speedypotato/chuni-lite/chunair-cad/IMG_20211214_130954.jpg

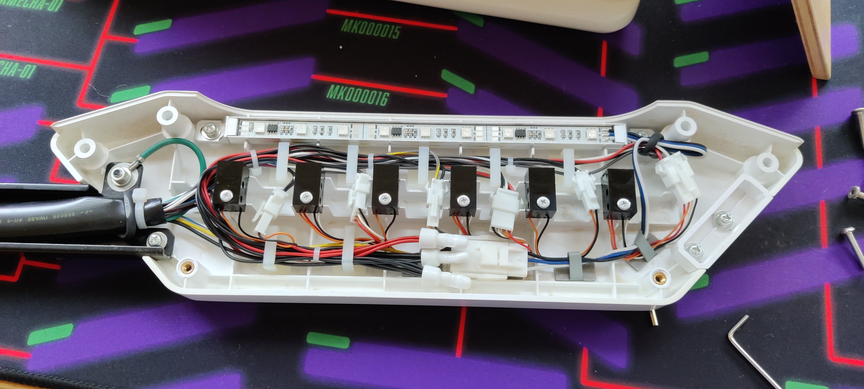
chunair-cad/IMG_20211214_130954.jpg
