speedypotato/chuni-lite/chunair-cad/IMG_20211214_131945.jpg

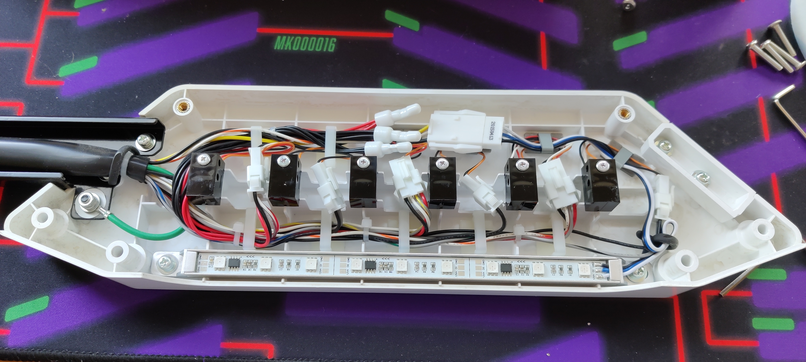
chunair-cad/IMG_20211214_131945.jpg
