speedypotato/chuni-lite/chunair-cad/IMG_20211214_160842.jpg

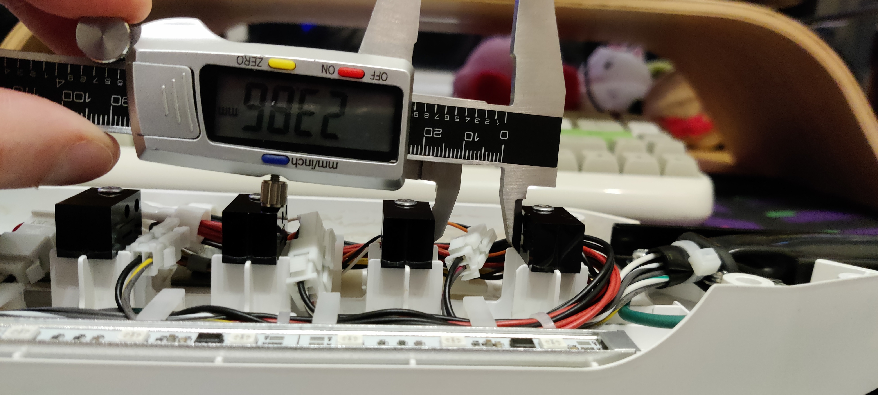
chunair-cad/IMG_20211214_160842.jpg
