speedypotato/chuni-lite/chunair-cad/IMG_20211214_160842__01.jpg

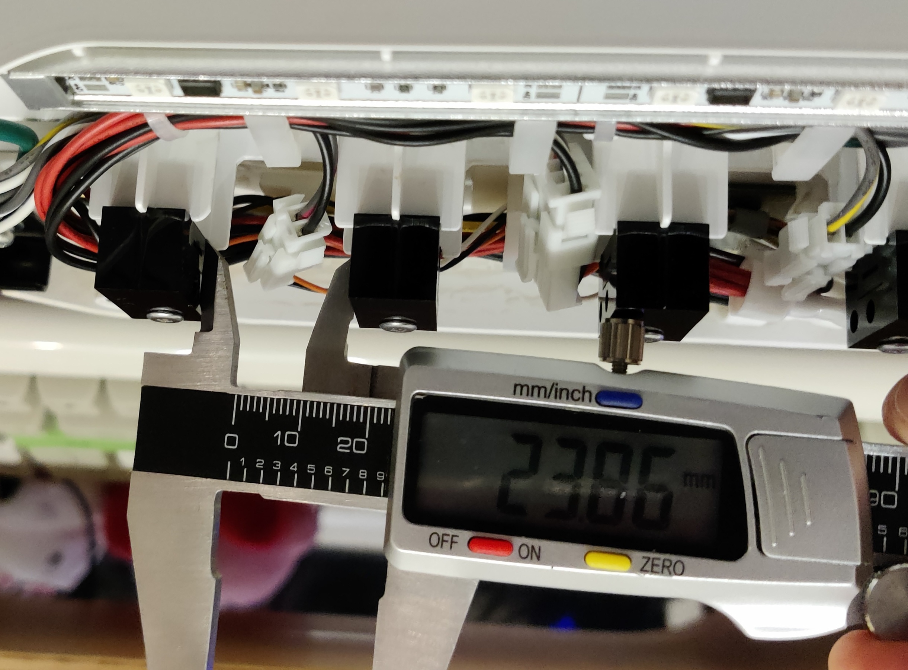
chunair-cad/IMG_20211214_160842__01.jpg
