speedypotato/chuni-lite/chunair-cad/IMG_20211214_161618.jpg

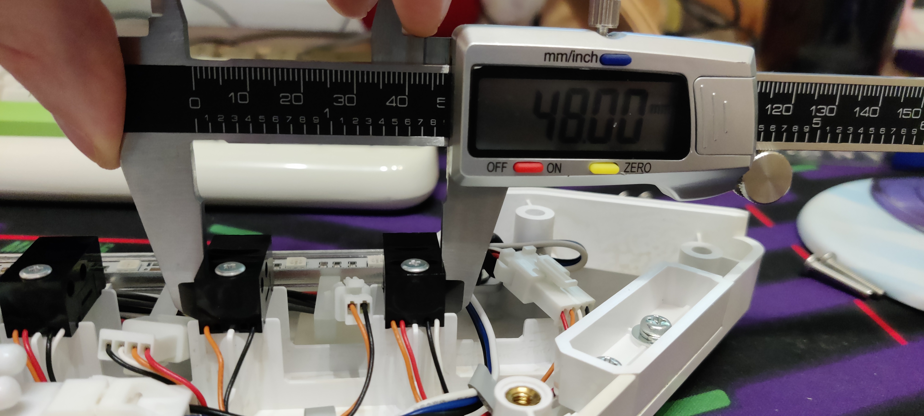
chunair-cad/IMG_20211214_161618.jpg
