speedypotato/chuni-lite/chunair-cad/airs/print/a12/bumper.3MF

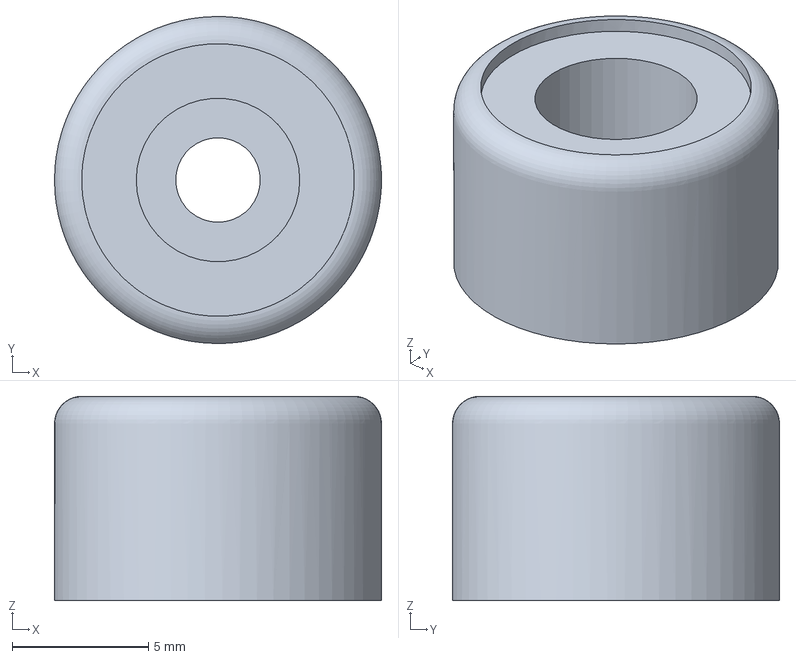
[picture p27: CAD file, 2022-03-22]
chunair-cad/airs/print/a12/bumper.3MF
12.0 x 12.0 x 7.50 mm
