speedypotato/chuni-lite/chunair-cad/airs/print/a3/slider.3MF

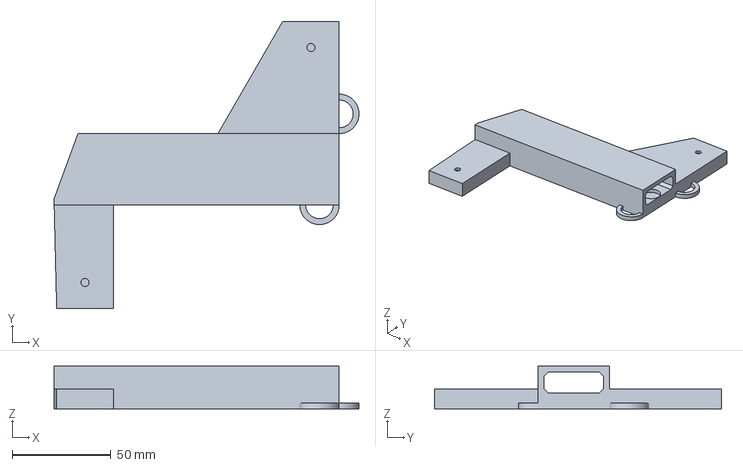
[picture p28: CAD file, 2022-02-23]
chunair-cad/airs/print/a3/slider.3MF
154.3 x 145.1 x 21.5 mm
