speedypotato/chuni-lite/chunair-cad/airs/print/a8/slider_rail.3MF

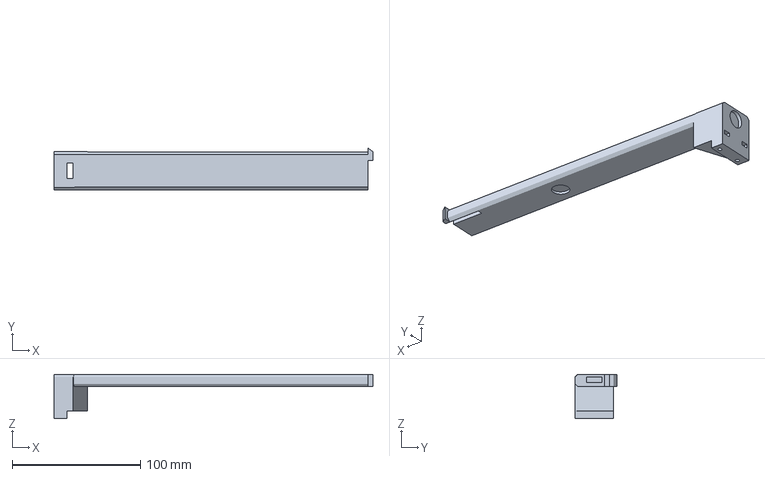
[picture p29: CAD file, 2022-02-23]
chunair-cad/airs/print/a8/slider_rail.3MF
249.0 x 33.0 x 34.5 mm
