speedypotato/chuni-lite/chunair/kicad-footprint-generator-master/scripts/Connector/Connector_JST/JST-PH-SMT-TOP_ENTRY.fcstd

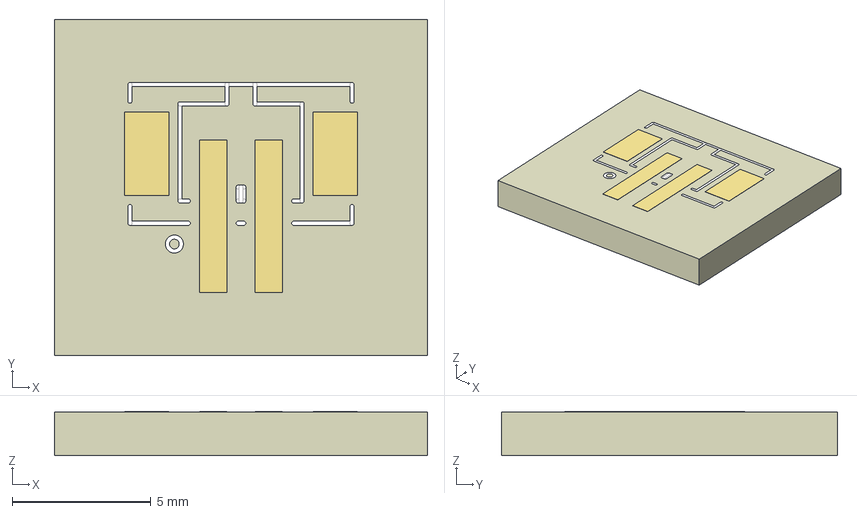
[picture p30: CAD file, 2022-02-25]
chunair/kicad-footprint-generator-master/scripts/Connector/Connector_JST/JST-PH-SMT-TOP_ENTRY.fcstd
13.4 x 12.1 x 1.60 mm
FrontSilk
TopPads
Pcb
