speedypotato/chuni-lite/chunair/kicad-footprint-generator-master/scripts/Connector/Connector_JST/JST-PH-SMT-SIDE_ENTRY.fcstd

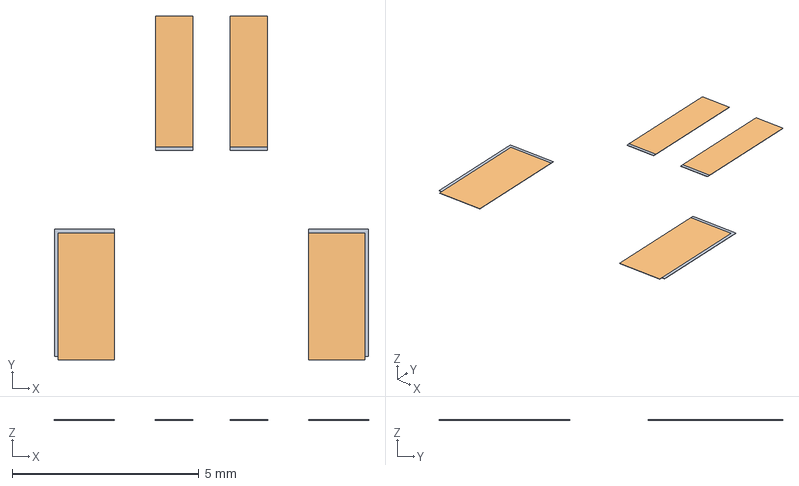
[picture p31: CAD file, 2022-02-25]
chunair/kicad-footprint-generator-master/scripts/Connector/Connector_JST/JST-PH-SMT-SIDE_ENTRY.fcstd
8.40 x 9.20 x 0.01 mm
TopPads
TopPads001
