speedypotato/chuni-lite/chunair-cad/parts/12x2mm_magnet.SLDPRT

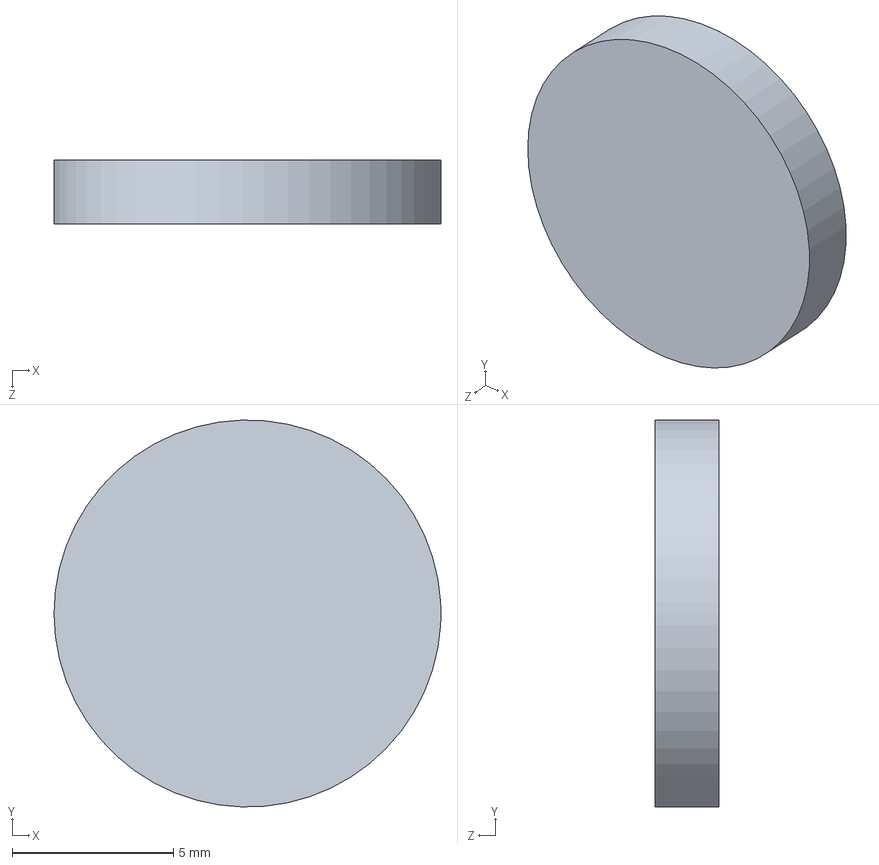
[picture p32: CAD file, 2022-02-10]
chunair-cad/parts/12x2mm_magnet.SLDPRT
12.0 x 12.0 x 2.00 mm
