speedypotato/chuni-lite/chunair/kicad-footprint-generator-master/scripts/Packages/Package_BGA/csp.yaml

WLCSP-12_1.403x1.555mm_P0.4mm_Stagger:
  description: "WLCSP-12, staggered array"
  size_source: "http://ww1.microchip.com/downloads/en/devicedoc/atmel-8235-8-bit-avr-microcontroller-attiny20_datasheet.pdf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"
  body_size_x: 1.403
  body_size_y: 1.555
  pitch_x: 0.2
  pitch_y: 0.346333
  pad_diameter: 0.215
  mask_margin: 0.0325
  paste_margin: 0.000001
  layout_x: 6
  layout_y: 4
  row_skips: [[2, 4, 6], [1, 3, 5], [2, 4, 6], [1, 3, 5]]
ST_WLCSP-25_Die425:
  description: "WLCSP-25"
  size_source: "http://www.st.com/resource/en/datasheet/stm32l031f6.pdf#page=112"
  body_size_x: 2.097
  body_size_y: 2.493
  pitch: 0.4
  pad_diameter: 0.22
  mask_margin: 0.04
  paste_margin: 0.000001
  layout_x: 5
  layout_y: 5
ST_WLCSP-25_Die444:
  description: "WLCSP-25"
  size_source: "http://www.st.com/resource/en/datasheet/stm32f031k6.pdf#page=93"
  body_size_x: 2.423
  body_size_y: 2.325
  pitch: 0.4
  pad_diameter: 0.225
  mask_margin: 0.0325
  paste_margin: 0.0125
  layout_x: 5
  layout_y: 5
ST_WLCSP-25_Die457:
  description: "WLCSP-25"
  size_source: "http://www.st.com/resource/en/datasheet/stm32l011k3.pdf#page=100"
  body_size_x: 2.133
  body_size_y: 2.070
  pitch: 0.4
  pad_diameter: 0.225
  mask_margin: 0.0325
  paste_margin: 0.0125
  layout_x: 5
  layout_y: 5
ST_WLCSP-36_Die417:
  description: "WLCSP-36"
  size_source: "http://www.st.com/resource/en/datasheet/stm32l052t8.pdf#page=123"
  body_size_x: 2.61
  body_size_y: 2.88
  pitch: 0.4
  pad_diameter: 0.22
  mask_margin: 0.04
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
  body_size_x: 5.537
  body_size_y: 6.095
  pitch: 0.4
  pad_diameter: 0.225
  mask_margin: 0.0325
  paste_margin: 0.0125
  layout_x: 13
  layout_y: 14
  row_skips: [[], [], [], [], [], [], [7], [7], [], [], [], [], [], []]
WLCSP-16_1.409x1.409mm_P0.35mm:
  description: "WLCSP-16"
  size_source: 'http://www.latticesemi.com/view_document?document_id=213'
  body_size_x: 1.409
  body_size_y: 1.409
  pitch: 0.35
  pad_diameter: 0.2
  layout_x: 4
  layout_y: 4
WLCSP-16_2.225x2.17mm_P0.5mm:
  description: "WLCSP-16 2.225x2.17mm"
  size_source: 'https://ww1.microchip.com/downloads/en/DeviceDoc/16B_WLCSP_CS_C04-06036c.pdf'
  body_size_x: 2.225
  body_size_y: 2.170
  pitch: 0.50
  pad_diameter: 0.327
  layout_x: 4
  layout_y: 4
WLCSP-8_1.551x2.284mm_P0.5mm:
  description: "WLCSP-8"
  size_source: "https://www.adestotech.com/wp-content/uploads/AT25SL321_112.pdf#page=75"
  body_size_x: 1.551
  body_size_y: 2.284
  pitch: 0.5
  pad_diameter: 0.2
  layout_x: 2
  layout_y: 4
WLCSP-4-X1-WLB0909-4_0.89x0.89mm_P0.5mm:
  description: "X1-WLB0909"
  size_source: 'https://www.diodes.com/assets/Datasheets/AP22913.pdf'
  body_size_x: 0.89
  body_size_y: 0.89
  pitch: 0.5
  pad_diameter: 0.235 # even though ball_diameter is 0.235 analog recommends a landing pad of 0.235
  layout_x: 2
  layout_y: 2
