speedypotato/chuni-lite/chunair/kicad-footprint-generator-master/scripts/Packages/Package_Gullwing__QFP_SOIC_SO/size_definitions/soic.yaml

FileHeader:
  library_Suffix: 'SO'
  device_type: 'SOIC'

SOIC-4_4.55x3.7mm_P2.54mm:
  custom_name_format: 'SOIC-4_4.55x3.7mm_P2.54mm' #does not take into account the excluded pins
  size_source: 'https://toshiba.semicon-storage.com/info/docget.jsp?did=11791&prodName=TLP185'
  body_size_x:
    minimum: 4.4
    nominal: 4.55
    maximum: 4.8
  body_size_y:
    minimum: 3.45
    nominal: 3.7
    maximum: 3.95
  overall_size_x:
    minimum: 6.6
    nominal: 7.0
    maximum: 7.4
  lead_width:
    nominal: 0.4
  lead_len:
    nominal: 0.5
  pitch: 1.27
  num_pins_x: 0
  num_pins_y: 3
  hidden_pins: [2, 5]

SOIC-4_4.55x2.6mm_P1.27mm:
  size_source: 'https://toshiba.semicon-storage.com/info/docget.jsp?did=12884&prodName=TLP291'
  body_size_x:
    minimum: 4.4
    nominal: 4.55
    maximum: 4.8
  body_size_y:
    minimum: 2.45
    nominal: 2.6
    maximum: 2.85
  overall_size_x:
    minimum: 6.6
    nominal: 7.0
    maximum: 7.4
  lead_width:
    minimum: 0.37
    maximum: 0.39
  lead_len:
    nominal: 0.5
  pitch: 1.27
  num_pins_x: 0
  num_pins_y: 2

SOIC-8_3.9x4.9mm_P1.27mm:
  size_source: 'JEDEC MS-012AA, https://www.analog.com/media/en/package-pcb-resources/package/pkg_pdf/soic_narrow-r/r_8.pdf'
  body_size_x: # from JEDEC
    nominal: 3.9
    tolerance: 0.1
  body_size_y:
    minimum: 4.8
    maximum: 5.0
  overall_height:
    minimum: 1.35
    maximum: 1.75

  overall_size_x: # from JEDEC (agrees with linked datasheet)
    nominal: 6
    tolerance: 0.2
  lead_len:
    minimum: 0.4
    maximum: 1.27
  lead_width: # from JEDEC (agrees with linked datasheet)
    minimum: 0.31
    maximum: 0.51

  pitch: 1.27
  num_pins_x: 0
  num_pins_y: 4

SOIC-8-1EP_3.9x4.9mm_P1.27mm_EP2.29x3.0mm:
  size_source: 'https://www.analog.com/media/en/technical-documentation/data-sheets/ada4898-1_4898-2.pdf#page=29'
  body_size_x:
    minimum: 3.8
    nominal: 3.9
    maximum: 4.0
  body_size_y:
    minimum: 4.8
    nominal: 4.9
    maximum: 5.0
  overall_height:
    minimum: 1.25
    maximum: 1.65

  overall_size_x:
    minimum: 5.8
    nominal: 6.0
    maximum: 6.2
  lead_len:
    minimum: 0.4
    maximum: 1.27
  lead_width:
    minimum: 0.31
    maximum: 0.51

  pitch: 1.27
  num_pins_x: 0
  num_pins_y: 4

  EP_size_x:
    nominal: 2.29
    tolerance: 0 # no tolerance given
  #EP_size_x_overwrite:
  #EP_mask_x:

  EP_size_y:
    nominal: 3.0 # 2.29+2*0.356 = 3.002 rounded to 3.0
    tolerance: 0 # no tolerance given
  #EP_size_y_overwrite:
  #EP_mask_y:

  # EP_paste_coverage: 0.65
  EP_num_paste_pads: [2, 2]

  thermal_vias:
    count: [2, 3]
    drill: 0.2
    # min_annular_ring: 0.15
    paste_via_clearance: 0.1
    EP_num_paste_pads: [2, 2]
    # paste_between_vias: 1
    # paste_rings_outside: 1
    EP_paste_coverage: 0.7
    grid: [1.3, 1]
    # bottom_pad_size:
    paste_avoid_via: False

SOIC-8-1EP_3.9x4.9mm_P1.27mm_EP2.41x3.81mm:
  size_source: 'https://www.analog.com/media/en/technical-documentation/data-sheets/ada4898-1_4898-2.pdf#page=29'
  body_size_x:
    minimum: 3.8
    nominal: 3.9
    maximum: 4.0
  body_size_y:
    minimum: 4.8
    nominal: 4.9
    maximum: 5.0
  overall_height:
    minimum: 1.25
    maximum: 1.65

  overall_size_x:
    minimum: 5.8
    nominal: 6.0
    maximum: 6.2
  lead_len:
    minimum: 0.4
    maximum: 1.27
  lead_width:
    minimum: 0.31
    maximum: 0.51

  pitch: 1.27
  num_pins_x: 0
  num_pins_y: 4

  EP_size_x:
    nominal: 2.41
    tolerance: 0 # no tolerance given
  # EP_size_x_overwrite: 2.41
  #EP_mask_x:

  EP_size_y:
    nominal: 3.81 # 3.098+2*0.356
    tolerance: 0 # no tolerance given
  # EP_size_y_overwrite: 3.1
  #EP_mask_y:

  # EP_paste_coverage: 0.65
  EP_num_paste_pads: [2, 2]

  thermal_vias:
    count: [2, 3]
    drill: 0.2
    # min_annular_ring: 0.15
    paste_via_clearance: 0.1
    EP_num_paste_pads: [2, 2]
    # paste_between_vias: 1
    # paste_rings_outside: 1
    EP_paste_coverage: 0.7
    grid: [1.4, 1.4]
    # bottom_pad_size:
    paste_avoid_via: False

SOIC-8-1EP_3.9x4.9mm_P1.27mm_EP2.41x3.1mm:
  size_source: 'http://www.ti.com/lit/ds/symlink/lm5017.pdf#page=31'
  body_size_x:
    minimum: 3.8
    maximum: 4.0
  body_size_y:
    minimum: 4.8
    maximum: 5.0
  overall_height:
    maximum: 1.7

  overall_size_x:
    minimum: 5.8
    maximum: 6.2
  lead_len:
    minimum: 0.4
    maximum: 1.27
  lead_width:
    minimum: 0.31
    maximum: 0.51

  pitch: 1.27
  num_pins_x: 0
  num_pins_y: 4

  EP_size_x:
    minimum: 2.11
    maximum: 2.71
  EP_size_x_overwrite: 2.95
  EP_mask_x: 2.71

  EP_size_y:
    minimum: 2.8
    maximum: 3.4
  EP_size_y_overwrite: 4.9
  EP_mask_y: 3.4

  # EP_paste_coverage: 0.65
  EP_num_paste_pads: [2, 2]

  thermal_vias:
    count: [2, 4]
    drill: 0.2
    # min_annular_ring: 0.15
    paste_via_clearance: 0.1
    EP_num_paste_pads: [2, 2]
    # paste_between_vias: 1
    # paste_rings_outside: 1
    EP_paste_coverage: 0.7
    grid: [1.3, 1.3]
    # bottom_pad_size:
    paste_avoid_via: False

SOIC-8-1EP_3.9x4.9mm_P1.27mm_EP2.41x3.3mm:
  size_source: 'http://www.allegromicro.com/~/media/Files/Datasheets/A4950-Datasheet.ashx#page=8'
  body_size_x:
    nominal: 3.9
    tolerance: 0.1
  body_size_y:
    nominal: 4.9
    tolerance: 0.1
  overall_height:
    maximum: 1.7

  overall_size_x:
    nominal: 6.0
    tolerance: 0.2
  lead_len:
    minimum: 0.4
    maximum: 1.27
  lead_width:
    minimum: 0.31
    maximum: 0.51

  pitch: 1.27
  num_pins_x: 0
  num_pins_y: 4

  EP_size_x:
    nominal: 2.41
    tolerance: 0 # no tolerance given
  # EP_size_x_overwrite: 2.41
  #EP_mask_x:

  EP_size_y:
    nominal: 3.3
    tolerance: 0 # no tolerance given
  # EP_size_y_overwrite: 3.1
  #EP_mask_y:

  # EP_paste_coverage: 0.65
  EP_num_paste_pads: [2, 2]

  thermal_vias:
    count: [2, 3]
    drill: 0.2
    # min_annular_ring: 0.15
    paste_via_clearance: 0.1
    EP_num_paste_pads: [2, 2]
    # paste_between_vias: 1
    # paste_rings_outside: 1
    EP_paste_coverage: 0.7
    grid: [1.4, 1.2]
    # bottom_pad_size:
    paste_avoid_via: False

SOIC-8-1EP_3.9x4.9mm_P1.27mm_EP2.514x3.2mm:
  size_source: 'https://www.renesas.com/eu/en/www/doc/datasheet/hip2100.pdf#page=13'
  body_size_x:
    minimum: 3.8 # rounded from 3.811
    maximum: 4.0 # rounded from 3.99
  body_size_y:
    minimum: 4.8
    maximum: 5.0 # rounded from 4.98
  overall_height:
    minimum: 1.43
    maximum: 1.68

  overall_size_x:
    minimum: 5.84
    maximum: 6.2
  lead_len:
    minimum: 0.41
    maximum: 0.89
  lead_width:
    minimum: 0.35
    maximum: 0.49

  pitch: 1.27
  num_pins_x: 0
  num_pins_y: 4

  EP_size_x:
    nominal: 2.514 # only maximum given but that is not supported by the script
    tolerance: 0
  # EP_size_x_overwrite:
  #EP_mask_x:

  EP_size_y:
    nominal: 3.2 # only maximum given but that is not supported by the script
    tolerance: 0
  # EP_size_y_overwrite:
  #EP_mask_y:

  # EP_paste_coverage: 0.65
  EP_num_paste_pads: [2, 2]

  thermal_vias:
    count: [2, 3]
    drill: 0.2
    # min_annular_ring: 0.15
    paste_via_clearance: 0.1
    EP_num_paste_pads: [2, 2]
    # paste_between_vias: 1
    # paste_rings_outside: 1
    EP_paste_coverage: 0.7
    grid: [1.4, 1.0]
    # bottom_pad_size:
    paste_avoid_via: False

    
       
SOIC-8-1EP_3.9x4.9mm_P1.27mm_EP2.62x3.51mm:
  size_source: 'https://www.monolithicpower.com/en/documentview/productdocument/index/version/2/document_type/Datasheet/lang/en/sku/MP2303A/document_id/494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'
  body_size_x:
    minimum: 3.8
    maximum: 4.0
  body_size_y:
    minimum: 4.8
    maximum: 5.0
  overall_height:
    minimum: 1.3
    maximum: 1.7

  overall_size_x:
    minimum: 5.8
    maximum: 6.2
  lead_len:
    minimum: 0.41
    maximum: 1.27
  lead_width:
    minimum: 0.33
    maximum: 0.51

  pitch: 1.27
  num_pins_x: 0
  num_pins_y: 4

  EP_size_x:
    minimum: 2.26
    maximum: 2.56

  EP_size_y:
    minimum: 3.15
    maximum: 3.45

  EP_size_x_overwrite: 2.62
  EP_size_y_overwrite: 3.51

  # EP_paste_coverage: 0.65
  EP_num_paste_pads: [2, 2]

  thermal_vias:
    count: [2, 3]
    drill: 0.2
    # min_annular_ring: 0.15
    paste_via_clearance: 0.1
    EP_num_paste_pads: [2, 2]
    # paste_between_vias: 1
    # paste_rings_outside: 1
    EP_paste_coverage: 0.7
    grid: [1.4, 1.0]
    # bottom_pad_size:
    paste_avoid_via: False

    
    
SOIC-8_5.23x5.23mm_P1.27mm:
  size_source: 'http://www.winbond.com/resource-files/w25q32jv%20revg%2003272018%20plus.pdf#page=68'
  body_size_x:
    minimum: 5.13
    nominal: 5.23
    maximum: 5.33
  body_size_y:
    minimum: 5.13
    nominal: 5.23
    maximum: 5.33
  overall_height:
    minimum: 1.75
    nominal: 1.95
    maximum: 2.16

  overall_size_x:
    minimum: 7.7
    nominal: 7.9
    maximum: 8.1
  lead_len:
    minimum: 0.5
    nominal: 0.65
    maximum: 0.8
  lead_width:
    minimum: 0.35
    nominal: 0.42
    maximum: 0.48

  pitch: 1.27
  num_pins_x: 0
  num_pins_y: 4

SOIC-8_5.275x5.275mm_P1.27mm:
  size_source: 'http://ww1.microchip.com/downloads/en/DeviceDoc/20005045C.pdf#page=23'
  body_size_x:
    minimum: 5.15
    maximum: 5.4
  body_size_y:
    minimum: 5.15
    maximum: 5.4
  overall_size_x:
    minimum: 7.7
    maximum: 8.1
  overall_height:
    minimum: 1.75
    maximum: 2.16
  lead_width:
    minimum: 0.35
    maximum: 0.5
  lead_len:
    minimum: 0.5
    maximum: 0.8

  pitch: 1.27
  num_pins_x: 0
  num_pins_y: 4

SOIC-8_7.5x5.85mm_P1.27mm:
  size_source: 'http://www.ti.com/lit/ml/mpds382b/mpds382b.pdf'
  body_size_x:
    minimum: 7.4
    maximum: 7.6
  body_size_y:
    minimum: 5.75
    maximum: 5.95
  overall_height:
    maximum: 2.8
  overall_size_x:
    nominal: 11.5
    tolerance: 0.25
  lead_len:
    minimum: 0.5
    maximum: 1.0
  lead_width:
    minimum: 0.31
    maximum: 0.51

  pitch: 1.27
  num_pins_x: 0
  num_pins_y: 4

SOIC-14_3.9x8.7mm_P1.27mm:
  #round to two significant digits to comply with old name
  custom_name_format: SOIC-{pincount}_{size_x:.2g}x{size_y:.2g}mm_P{pitch:g}mm
  size_source: 'JEDEC MS-012AB, https://www.analog.com/media/en/package-pcb-resources/package/pkg_pdf/soic_narrow-r/r_14.pdf'
  body_size_x: # from JEDEC
    nominal: 3.9
    tolerance: 0.1
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
    minimum: 2.35
    maximum: 2.65

  overall_size_x: # from JEDEC
    nominal: 10.3
    tolerance: 0.33
  lead_len:
    minimum: 0.4
    maximum: 1.27
  lead_width: # from JEDEC (agrees with linked datasheet)
    minimum: 0.31
    maximum: 0.51

  pitch: 1.27
  num_pins_x: 0
  num_pins_y: 14

SOIC-28W_7.5x18.7mm_P1.27mm:
  #round to two significant digits to comply with old name
  custom_name_format: SOIC-{pincount}W_{size_x:.2g}x{size_y:.3g}mm_P{pitch:g}mm
  size_source: 'https://www.akm.com/akm/en/file/datasheet/AK5394AVS.pdf#page=23'
  body_size_x:
    nominal: 7.5
    tolerance: 0.2
  body_size_y:
    nominal: 18.7
    tolerance: 0.3
  overall_height:
    nominal: 2.2
    tolerance: 0.1

  overall_size_x:
    nominal: 10.4
    tolerance: 0.3
  lead_len:
    nominal: 0.75
    tolerance: 0.2
  lead_width:
    nominal: 0.4
    tolerance: 0.1

  pitch: 1.27
  num_pins_x: 0
  num_pins_y: 14
