speedypotato/chuni-lite/chunair/kicad-footprint-generator-master/scripts/Packages/Package_Gullwing__QFP_SOIC_SO/size_definitions/tssop.yaml

FileHeader:
  library_Suffix: 'SO'
  device_type: 'TSSOP'

##############################################################################
# TSSOP Variations - 0.40 PITCH
# BODY WIDTH (E1) = 4.40 NOM
##############################################################################

TSSOP-14_4.4x3.6mm_P0.4mm:
  size_source: 'JEDEC MO-194 Var AA https://www.jedec.org/document_search?search_api_views_fulltext=MO-194'
  body_size_x: 4.4 +/-0.1
  body_size_y: 3.6 +/-0.1
  overall_size_x: 6.4
  body_height: 1.2
  lead_width: 0.13 .. 0.23
  lead_len: 0.6 +/-0.15
  pitch: 0.4
  num_pins_x: 0
  num_pins_y: 7

TSSOP-16_4.4x3.6mm_P0.4mm:
  size_source: 'JEDEC MO-194 Var AB https://www.jedec.org/document_search?search_api_views_fulltext=MO-194'
  body_size_x: 4.4 +/-0.1
  body_size_y: 3.6 +/-0.1
  overall_size_x: 6.4
  body_height: 1.2
  lead_width: 0.13 .. 0.23
  lead_len: 0.6 +/-0.15
  pitch: 0.4
  num_pins_x: 0
  num_pins_y: 8

TSSOP-20_4.4x5mm_P0.4mm:
  size_source: 'JEDEC MO-194 Var AC https://www.jedec.org/document_search?search_api_views_fulltext=MO-194'
  body_size_x: 4.4 +/-0.1
  body_size_y: 5.0 +/-0.1
  overall_size_x: 6.4
  body_height: 1.2
  lead_width: 0.13 .. 0.23
  lead_len: 0.6 +/-0.15
  pitch: 0.4
  num_pins_x: 0
  num_pins_y: 10

TSSOP-24_4.4x5mm_P0.4mm:
  size_source: 'JEDEC MO-153 Var CA https://www.jedec.org/document_search?search_api_views_fulltext=MO-153'
  body_size_x: 4.4 +/-0.1
  body_size_y: 5.0 +/-0.1
  overall_size_x: 6.4
  body_height: 1.2
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
  body_size_x: 8.0 +/-0.1
  body_size_y: 12.5 +/-0.1
  overall_size_x: 10.0
  body_height: 1.2
  lead_width: 0.17 .. 0.30
  lead_len: 0.6 +/-0.15
  pitch: 0.5
  num_pins_x: 0
  num_pins_y: 24

TSSOP-56_8x14mm_P0.5mm:
  size_source: 'JEDEC MO-153 Var HD https://www.jedec.org/document_search?search_api_views_fulltext=MO-153'
  body_size_x: 8.0 +/-0.1
  body_size_y: 14.0 +/-0.1
  overall_size_x: 10.0
  body_height: 1.2
  lead_width: 0.17 .. 0.30
  lead_len: 0.6 +/-0.15
  pitch: 0.5
  num_pins_x: 0
  num_pins_y: 28

##############################################################################
# TSSOP Variations - 0.65 PITCH
# BODY WIDTH (E1) = 4.40 NOM
##############################################################################

TSSOP-8_4.4x3mm_P0.65mm:
  size_source: 'JEDEC MO-153 Var AA https://www.jedec.org/document_search?search_api_views_fulltext=MO-153'
  body_size_x: 4.4 +/-0.1
  body_size_y: 3.0 +/-0.1
  overall_size_x: 6.4
  body_height: 1.2
  lead_width: 0.17 .. 0.30
  lead_len: 0.6 +/-0.15
  pitch: 0.65
  num_pins_x: 0
  num_pins_y: 4

TSSOP-16_4.4x5mm_P0.65mm:
  size_source: 'JEDEC MO-153 Var AB https://www.jedec.org/document_search?search_api_views_fulltext=MO-153'
  body_size_x: 4.4 +/-0.1
  body_size_y: 5.0 +/-0.1
  overall_size_x: 6.4
  body_height: 1.2
  lead_width: 0.17 .. 0.30
  lead_len: 0.6 +/-0.15
  pitch: 0.65
  num_pins_x: 0
  num_pins_y: 8

TSSOP-16-1EP_4.4x5mm_P0.65mm_EP3x3mm:
  size_source: 'Allegro A4954 https://www.allegromicro.com/-/media/Files/Datasheets/A4954-Datasheet.ashx'
  body_size_x: 4.4 +/-0.1
  body_size_y: 5.0 +/-0.1
  overall_size_x: 6.4 +/-0.2
  body_height: 1.2
  lead_width: 0.19 .. 0.30
  lead_len: 0.6 +/-0.15
  pitch: 0.65
  num_pins_x: 0
  num_pins_y: 8
  EP_size_x:
    nominal: 3
  EP_size_y:
    nominal: 3
  EP_num_paste_pads: [2, 2]
  thermal_vias:
    count: [2, 2]
    drill: 0.3
    paste_avoid_via: false
    EP_num_paste_pads: [2, 2]

TSSOP-14_4.4x5mm_P0.65mm:
  size_source: 'JEDEC MO-153 Var AB-1 https://www.jedec.org/document_search?search_api_views_fulltext=MO-153'
  body_size_x: 4.4 +/-0.1
  body_size_y: 5.0 +/-0.1
  overall_size_x: 6.4
  body_height: 1.2
  lead_width: 0.17 .. 0.30
  lead_len: 0.6 +/-0.15
  pitch: 0.65
  num_pins_x: 0
  num_pins_y: 7

TSSOP-20_4.4x6.5mm_P0.65mm:
  size_source: 'JEDEC MO-153 Var AC https://www.jedec.org/document_search?search_api_views_fulltext=MO-153'
  body_size_x: 4.4 +/-0.1
  body_size_y: 6.5 +/-0.1
  overall_size_x: 6.4
  body_height: 1.2
  lead_width: 0.17 .. 0.30
  lead_len: 0.6 +/-0.15
  pitch: 0.65
  num_pins_x: 0
  num_pins_y: 10

TSSOP-24_4.4x7.8mm_P0.65mm:
  size_source: 'JEDEC MO-153 Var AD https://www.jedec.org/document_search?search_api_views_fulltext=MO-153'
  body_size_x: 4.4 +/-0.1
  body_size_y: 7.8 +/-0.1
  overall_size_x: 6.4
  body_height: 1.2
  lead_width: 0.17 .. 0.30
  lead_len: 0.6 +/-0.15
  pitch: 0.65
  num_pins_x: 0
  num_pins_y: 12

TSSOP-24-1EP_4.4x7.8mm_P0.65mm_EP3.2x5mm:
  size_source: 'https://www.st.com/resource/en/datasheet/led1642gw.pdf#page=37'
  
  body_size_x:
    minimum: 4.30 
    nominal: 4.40 
    maximum: 4.50 
  body_size_y:
    minimum: 7.70
    nominal: 7.80
    maximum: 7.90

  overall_size_x: 
    minimum: 6.30
    nominal: 6.40
    maximum: 6.50

  body_height: 1.20

  lead_width: 0.19 .. 0.30

  lead_len: 
    minimum: 0.45
    nominal: 0.60
    maximum: 0.75

  pitch: 0.65

  num_pins_x: 0
  num_pins_y: 12

  EP_size_x:
    minimum: 3.00
    nominal: 3.20
    maximum: 3.40
  EP_size_y:
    minimum: 4.80
    nominal: 5.00
    maximum: 5.20
  EP_num_paste_pads: [2, 3]

TSSOP-28_4.4x9.7mm_P0.65mm:
  size_source: 'JEDEC MO-153 Var AE https://www.jedec.org/document_search?search_api_views_fulltext=MO-153'
  body_size_x: 4.4 +/-0.1
  body_size_y: 9.7 +/-0.1
  overall_size_x: 6.4
  body_height: 1.2
  lead_width: 0.17 .. 0.30
  lead_len: 0.6 +/-0.15
  pitch: 0.65
  num_pins_x: 0
  num_pins_y: 14

TSSOP-28-1EP_4.4x9.7mm_P0.65mm_EP2.85x6.7mm:
  size_source: 'JEDEC MO-153 Var AET Pkg.Code U28E-4 https://pdfserv.maximintegrated.com/package_dwgs/21-0108.PDF'
  
  body_size_x:
    minimum: 4.30 
    maximum: 4.50 
  body_size_y:
    minimum: 9.60
    maximum: 9.80

  overall_size_x: 
    minimum: 6.25
    maximum: 6.50

  body_height:
    maximum: 1.10

  lead_width:
    minimum: 0.19
    maximum: 0.30

  lead_len: 
    minimum: 0.50
    maximum: 0.70

  pitch: 0.65

  num_pins_x: 0
  num_pins_y: 14

  EP_size_x:
    minimum: 2.60
    maximum: 3.10
  EP_size_y:
    minimum: 6.50
    maximum: 6.90
  EP_num_paste_pads: [2, 3]

##############################################################################
# TSSOP Variations - 0.65 PITCH
# BODY WIDTH (E1) = 6.10 NOM
##############################################################################

TSSOP-24_6.1x7.8mm_P0.65mm:
  size_source: 'JEDEC MO-153 Var DA https://www.jedec.org/document_search?search_api_views_fulltext=MO-153'
  body_size_x: 6.1 +/-0.1
  body_size_y: 7.8 +/-0.1
  overall_size_x: 8.1
  body_height: 1.2
  lead_width: 0.17 .. 0.30
  lead_len: 0.6 +/-0.15
  pitch: 0.65
  num_pins_x: 0
  num_pins_y: 12

TSSOP-28_6.1x9.7mm_P0.65mm:
  size_source: 'JEDEC MO-153 Var DB https://www.jedec.org/document_search?search_api_views_fulltext=MO-153'
  body_size_x: 6.1 +/-0.1
  body_size_y: 9.7 +/-0.1
  overall_size_x: 8.1
  body_height: 1.2
  lead_width: 0.17 .. 0.30
  lead_len: 0.6 +/-0.15
  pitch: 0.65
  num_pins_x: 0
  num_pins_y: 14

TSSOP-30_6.1x9.7mm_P0.65mm:
  size_source: 'JEDEC MO-153 Var DB-1 https://www.jedec.org/document_search?search_api_views_fulltext=MO-153'
  body_size_x: 6.1 +/-0.1
  body_size_y: 9.7 +/-0.1
  overall_size_x: 8.1
  body_height: 1.2
  lead_width: 0.17 .. 0.30
  lead_len: 0.6 +/-0.15
  pitch: 0.65
  num_pins_x: 0
  num_pins_y: 15

TSSOP-32_6.1x11mm_P0.65mm:
  size_source: 'JEDEC MO-153 Var DC https://www.jedec.org/document_search?search_api_views_fulltext=MO-153'
  body_size_x: 6.1 +/-0.1
  body_size_y: 11.0 +/-0.1
  overall_size_x: 8.1
  body_height: 1.2
  lead_width: 0.17 .. 0.30
  lead_len: 0.6 +/-0.15
  pitch: 0.65
  num_pins_x: 0
  num_pins_y: 16

TSSOP-36_6.1x12.5mm_P0.65mm:
  size_source: 'JEDEC MO-153 Var DD https://www.jedec.org/document_search?search_api_views_fulltext=MO-153'
  body_size_x: 6.1 +/-0.1
  body_size_y: 12.5 +/-0.1
  overall_size_x: 8.1
  body_height: 1.2
  lead_width: 0.17 .. 0.30
  lead_len: 0.6 +/-0.15
  pitch: 0.65
  num_pins_x: 0
  num_pins_y: 18

TSSOP-38_6.1x12.5mm_P0.65mm:
  size_source: 'JEDEC MO-153 Var DD-1 https://www.jedec.org/document_search?search_api_views_fulltext=MO-153'
  body_size_x: 6.1 +/-0.1
  body_size_y: 12.5 +/-0.1
  overall_size_x: 8.1
  body_height: 1.2
  lead_width: 0.17 .. 0.30
  lead_len: 0.6 +/-0.15
  pitch: 0.65
  num_pins_x: 0
  num_pins_y: 19

TSSOP-40_6.1x14mm_P0.65mm:
  size_source: 'JEDEC MO-153 Var DE https://www.jedec.org/document_search?search_api_views_fulltext=MO-153'
  body_size_x: 6.1 +/-0.1
  body_size_y: 14.0 +/-0.1
  overall_size_x: 8.1
  body_height: 1.2
  lead_width: 0.17 .. 0.30
  lead_len: 0.6 +/-0.15
  pitch: 0.65
  num_pins_x: 0
  num_pins_y: 20

##############################################################################
# TSSOP Variations - 0.65 PITCH
# BODY WIDTH (E1) = 8.0 NOM
##############################################################################

TSSOP-28_8x9.7mm_P0.65mm:
  size_source: 'JEDEC MO-153 Var GA https://www.jedec.org/document_search?search_api_views_fulltext=MO-153'
  body_size_x: 8.0 +/-0.1
  body_size_y: 9.7 +/-0.1
  overall_size_x: 10.0
  body_height: 1.2
  lead_width: 0.17 .. 0.30
  lead_len: 0.6 +/-0.15
  pitch: 0.65
  num_pins_x: 0
  num_pins_y: 14

TSSOP-32_8x11mm_P0.65mm:
  size_source: 'JEDEC MO-153 Var GB https://www.jedec.org/document_search?search_api_views_fulltext=MO-153'
  body_size_x: 8.0 +/-0.1
  body_size_y: 11.0 +/-0.1
  overall_size_x: 10.0
  body_height: 1.2
  lead_width: 0.17 .. 0.30
  lead_len: 0.6 +/-0.15
  pitch: 0.65
  num_pins_x: 0
  num_pins_y: 16

TSSOP-36_8x12.5mm_P0.65mm:
  size_source: 'JEDEC MO-153 Var GC https://www.jedec.org/document_search?search_api_views_fulltext=MO-153'
  body_size_x: 8.0 +/-0.1
  body_size_y: 12.5 +/-0.1
  overall_size_x: 10.0
  body_height: 1.2
  lead_width: 0.17 .. 0.30
  lead_len: 0.6 +/-0.15
  pitch: 0.65
  num_pins_x: 0
  num_pins_y: 18

TSSOP-40_8x14mm_P0.65mm:
  size_source: 'JEDEC MO-153 Var GD https://www.jedec.org/document_search?search_api_views_fulltext=MO-153'
  body_size_x: 8.0 +/-0.1
  body_size_y: 14.0 +/-0.1
  overall_size_x: 10.0
  body_height: 1.2
  lead_width: 0.17 .. 0.30
  lead_len: 0.6 +/-0.15
  pitch: 0.65
  num_pins_x: 0
  num_pins_y: 20

##############################################################################
# TSSOP Variations - 4.0 PITCH
# BODY WIDTH (E1) = 5.0 NOM
##############################################################################

TSSOP-4_4.4x5.0mm_P4.0mm:
  size_source: 'https://www.onsemi.com/pub/Collateral/MDB8S-D.PDF#page=4'
  body_size_x: 4.25 .. 4.55
  body_size_y: 4.85 .. 5.15
  overall_size_x: 6.3 .. 6.7
  body_height: 1.75
  lead_width: 0.6 .. 0.7
  lead_len: 0.5 .. 0.7
  pitch: 4.0
  num_pins_x: 0
  num_pins_y: 2
