speedypotato/chuni-lite/chunair/kicad-footprint-generator-master/scripts/Packages/Package_Gullwing__QFP_SOIC_SO/size_definitions/hsop.yaml

FileHeader:
  library_Suffix: 'SO'
  device_type: 'HSOP'

HSOP-8-1EP_3.9x4.9mm_P1.27mm_EP2.41x3.1mm_ThermalVias:
  size_source: 'https://www.st.com/resource/en/datasheet/l5973d.pdf'
  body_size_x:
    nominal: 3.9
    tolerance: 0.1
  body_size_y:
    nominal: 4.9
    tolerance: 0.1
  overall_size_x:
    nominal: 6
    tolerance: 0.2
  lead_width:
    nominal: 0.42
    tolerance: [0.04, 0.05]
  lead_len:
    nominal: 0.65
    tolerance: 0.15
  pitch: 1.27
  num_pins_x: 0
  num_pins_y: 4


  EP_size_x:
    nominal: 2.41
    tolerance: 0.1
  EP_size_y:
    nominal: 3.1
    tolerance: 0.1
  # EP_paste_coverage: 0.65
  EP_num_paste_pads: [2, 2]
  #heel_reduction: 0.1 #for relatively large EP pads (increase clearance)
  # EP_size_limit_x: 3.6  #for relatively large EP pads (increase clearance)
  # EP_size_limit_y: 3.6  #for relatively large EP pads (increase clearance)

  thermal_vias:
    count: [2, 3]
    drill: 0.2
    # min_annular_ring: 0.15
    paste_via_clearance: 0.1
    EP_num_paste_pads: [2, 2]
    # paste_between_vias: 1
    # paste_rings_outside: 1
    EP_paste_coverage: 0.65
    # grid: [1.5, 1.5]
    # bottom_pad_size:
    paste_avoid_via: False

HSOP-8-1EP_3.9x4.9mm_P1.27mm_EP2.3x2.3mm_ThermalVias:
  size_source: 'https://www.st.com/resource/en/datasheet/l7980.pdf'
  body_size_x:
    nominal: 3.9
    tolerance: 0.1
  body_size_y:
    nominal: 4.9
    tolerance: 0.1
  overall_size_x:
    nominal: 6
    tolerance: 0.2
  lead_width:
    minimum: 0.31
    maximum: 0.51
  lead_len:
    minimum: 0.40
    maximum: 1.27
  pitch: 1.27
  num_pins_x: 0
  num_pins_y: 4


  EP_size_x:
    nominal: 2.3
  EP_size_y:
    nominal: 2.3
  EP_num_paste_pads: [2, 2]

  thermal_vias:
    count: [2, 2]
    drill: 0.2
    # min_annular_ring: 0.15
    paste_via_clearance: 0.1
    EP_num_paste_pads: [2, 2]
    # paste_between_vias: 1
    # paste_rings_outside: 1
    EP_paste_coverage: 0.65
    # grid: [1.5, 1.5]
    # bottom_pad_size:
    paste_avoid_via: False

HSOP-32-1EP_7.5x11.0mm_P0.65mm_EP4.7x4.7mm:
  size_source: 'https://www.nxp.com/docs/en/package-information/SOT1746-3.pdf'
  body_size_x:
    minimum: 7.4
    maximum: 7.6
  body_size_y:
    minimum: 10.9
    maximum: 11.1
  overall_size_x:
    nominal: 10.3
    tolerance: 0
  lead_width:
    minimum: 0.22
    maximum: 0.38
  lead_len:
    minimum: 0.5
    maximum: 0.9
  pitch: 0.65
  num_pins_x: 0
  num_pins_y: 16


  EP_size_x:
    nominal: 4.7
    tolerance: 0
  EP_size_y:
    nominal: 4.7
    tolerance: 0
  EP_num_paste_pads: [2, 2]

HSOP-54-1EP_7.5x17.9mm_P0.65mm_EP4.6x4.6mm:
  size_source: 'https://www.nxp.com/docs/en/package-information/98ASA10506D.pdf'
  body_size_x:
    minimum: 7.4
    maximum: 7.6
  body_size_y:
    minimum: 17.8
    maximum: 18.0
  overall_size_x:
    nominal: 10.3
    tolerance: 0
  lead_width:
    minimum: 0.22
    maximum: 0.38
  lead_len:
    minimum: 0.5
    maximum: 0.9
  pitch: 0.65
  num_pins_x: 0
  num_pins_y: 27


  EP_size_x:
    minimum: 3.9
    maximum: 5.3
  EP_size_y:
    minimum: 3.9
    maximum: 5.3
  EP_num_paste_pads: [2, 2]
