speedypotato/chuni-lite/chunair/kicad-footprint-generator-master/scripts/Packages/Package_NoLead__DFN_QFN_LGA_SON/size_definitions/qfn/hvqfn.yaml

HVQFN-16-1EP_3x3mm_P0.5mm_EP1.5x1.5mm:
  device_type: 'HVQFN'
  #manufacturer: 'NXP'
  #part_number: 'SOT758-1'
  size_source: 'https://www.nxp.com/docs/en/package-information/SOT758-1.pdf'
  ipc_class: 'qfn'
  body_size_x:
    minimum: 2.9
    nominal: 3.0
    maximum: 3.1
  body_size_y:
    minimum: 2.9
    nominal: 3.0
    maximum: 3.1
  overall_height:
    maximum: 1
  lead_width:
    minimum: 0.18
    maximum: 0.3
  lead_len:
    minimum: 0.3
    maximum: 0.5

  EP_size_x:
    minimum: 1.45
    maximum: 1.75
  EP_size_y:
    minimum: 1.45
    maximum: 1.75
  EP_size_x_overwrite: 1.5
  EP_size_y_overwrite: 1.5
  EP_num_paste_pads: [2, 2]

  pitch: 0.5
  num_pins_x: 4
  num_pins_y: 4

HVQFN-24-1EP_4x4mm_P0.5mm_EP2.5x2.5mm:
  device_type: 'HVQFN'
  size_source: 'https://www.nxp.com/docs/en/package-information/SOT616-3.pdf'
  ipc_class: 'qfn' # 'qfn_pull_back'
  body_size_x:
    minimum: 3.9
    nominal: 4.0
    maximum: 4.1
  body_size_y:
    minimum: 3.9
    nominal: 4.0
    maximum: 4.1
  overall_height:
    maximum: 1
  lead_width:
    minimum: 0.18
    maximum: 0.3
  lead_len:
    minimum: 0.3
    maximum: 0.5

  EP_size_x:
    minimum: 2.45
    maximum: 2.75
  EP_size_y:
    minimum: 2.45
    maximum: 2.75
  EP_size_x_overwrite: 2.5
  EP_size_y_overwrite: 2.5
  EP_num_paste_pads: [2, 2]

  thermal_vias:
    count: [3, 3]
    drill: 0.2
    paste_via_clearance: 0.1
    EP_paste_coverage: 0.55
  pitch: 0.5
  num_pins_x: 6
  num_pins_y: 6

HVQFN-24-1EP_4x4mm_P0.5mm_EP2.6x2.6mm:
  device_type: 'HVQFN'
  size_source: 'https://www.nxp.com/docs/en/package-information/SOT616-3.pdf'
  ipc_class: 'qfn' # 'qfn_pull_back'
  body_size_x:
    minimum: 3.9
    nominal: 4.0
    maximum: 4.1
  body_size_y:
    minimum: 3.9
    nominal: 4.0
    maximum: 4.1
  overall_height:
    maximum: 1
  lead_width:
    minimum: 0.18
    maximum: 0.3
  lead_len:
    minimum: 0.3
    maximum: 0.5

  EP_size_x:
    minimum: 2.45
    maximum: 2.75
  EP_size_y:
    minimum: 2.45
    maximum: 2.75
  EP_num_paste_pads: [3, 3]

  thermal_vias:
    count: [3, 3]
    drill: 0.2
    paste_via_clearance: 0.1
    EP_paste_coverage: 0.55
  pitch: 0.5
  num_pins_x: 6
  num_pins_y: 6
  
HVQFN-24-1EP_4x4mm_P0.5mm_EP2.1x2.1mm:
  device_type: 'HVQFN'
  size_source: 'https://www.nxp.com/docs/en/package-information/SOT616-1.pdf'
  ipc_class: 'qfn' # 'qfn_pull_back'
  body_size_x:
    minimum: 3.9
    nominal: 4.0
    maximum: 4.1
  body_size_y:
    minimum: 3.9
    nominal: 4.0
    maximum: 4.1
  overall_height:
    maximum: 1
  lead_width:
    minimum: 0.18
    maximum: 0.3
  lead_len:
    minimum: 0.3
    maximum: 0.5

  EP_size_x:
    minimum: 1.95
    maximum: 2.25
  EP_size_y:
    minimum: 1.95
    maximum: 2.25
  EP_num_paste_pads: [3, 3]

  pitch: 0.5
  num_pins_x: 6
  num_pins_y: 6


HVQFN-32-1EP_5x5mm_P0.5mm_EP3.1x3.1mm:
  device_type: 'HVQFN'
  size_source: 'https://www.nxp.com/docs/en/package-information/SOT617-1.pdf'
  ipc_class: 'qfn'
  body_size_x:
    minimum: 4.9
    nominal: 5.0
    maximum: 5.1
  body_size_y:
    minimum: 4.9
    nominal: 5.0
    maximum: 5.1
  overall_height:
    maximum: 1
  lead_width:
    minimum: 0.18
    maximum: 0.3
  lead_len:
    minimum: 0.3
    maximum: 0.5

  EP_size_x:
    minimum: 2.95
    maximum: 3.25
  EP_size_y:
    minimum: 2.95
    maximum: 3.25
  EP_num_paste_pads: [3, 3]

  thermal_vias:
    count: [4, 4]
    drill: 0.2
    paste_via_clearance: 0.1
    EP_paste_coverage: 0.55
  pitch: 0.5
  num_pins_x: 8
  num_pins_y: 8

HVQFN-40-1EP_6x6mm_P0.5mm_EP4.1x4.1mm:
  device_type: 'HVQFN'
  size_source: 'https://www.nxp.com/docs/en/package-information/SOT618-1.pdf'
  ipc_class: 'qfn' # 'qfn_pull_back'
  body_size_x:
    minimum: 5.9
    nominal: 6.0
    maximum: 6.1
  body_size_y:
    minimum: 5.9
    nominal: 6.0
    maximum: 6.1
  overall_height:
    minimum: 0.8
    nominal: 0.85
    maximum: 1
  lead_width:
    minimum: 0.18
    nominal: 0.21
    maximum: 0.3
  lead_len:
    minimum: 0.3
    nominal: 0.4
    maximum: 0.5

  EP_size_x:
    minimum: 3.95
    maximum: 4.25
  EP_size_y:
    minimum: 3.95
    maximum: 4.25
  EP_num_paste_pads: [3, 3]

  thermal_vias:
    count: [4, 4]
    drill: 0.2
    paste_via_clearance: 0.1
    EP_paste_coverage: 0.6
  pitch: 0.5
  num_pins_x: 10
  num_pins_y: 10
