speedypotato/chuni-lite/chunair/kicad-footprint-generator-master/scripts/Packages/Package_Gullwing__QFP_SOIC_SO/size_definitions/sot.yaml

FileHeader:
  library_Suffix: 'TO_SOT_SMD'
  device_type: 'SOT'

SOT-23:
  size_source: 'https://www.jedec.org/system/files/docs/to-236h.pdf variant AB'
  custom_name_format: 'SOT-23'
  body_size_x: 1.20 .. 1.30 .. 1.40
  body_size_y: 2.8 .. 2.9 .. 3.04
  overall_size_x: 2.10 .. 2.64
  lead_width: 0.3 .. 0.5
  lead_len: 0.40 .. 0.50 .. 0.6
  pitch: 0.95
  num_pins_x: 0
  num_pins_y: 3
  deleted_pins: [2, 4, 6]

SOT-23-5:
  size_source: 'https://www.jedec.org/sites/default/files/docs/Mo-178c.PDF variant AA'
  custom_name_format: 'SOT-23-5'
  body_size_x: 1.6
  body_size_y: 2.9
  overall_size_x: 2.8
  lead_width: 0.3 .. 0.5
  lead_len: 0.3 .. 0.45 .. 0.6
  pitch: 0.95
  num_pins_x: 0
  num_pins_y: 3
  deleted_pins: [5]

SOT-23-6:
  size_source: 'https://www.jedec.org/sites/default/files/docs/Mo-178c.PDF variant AB'
  custom_name_format: 'SOT-23-6'
  body_size_x: 1.6
  body_size_y: 2.9
  overall_size_x: 2.8
  lead_width: 0.3 .. 0.5
  lead_len: 0.3 .. 0.45 .. 0.6
  pitch: 0.95
  num_pins_x: 0
  num_pins_y: 3
  
SOT-23-8:
  size_source: 'https://www.jedec.org/sites/default/files/docs/Mo-178c.PDF variant BA'
  custom_name_format: 'SOT-23-8'
  body_size_x: 1.6
  body_size_y: 2.9
  overall_size_x: 2.8
  lead_width: 0.22 .. 0.38
  lead_len: 0.3 .. 0.45 .. 0.6
  pitch: 0.65
  num_pins_x: 0
  num_pins_y: 4
