speedypotato/chuni-lite/chunair/kicad-footprint-generator-master/scripts/TerminalBlock_Altech/Altech.yml

AK300:
  description: "Altech AK300 serie terminal block"
  datasheet: "http://www.altechcorp.com/PDFS/PCBMETRC.PDF"
  tags: "Altech AK300 serie connector"
  manufacture: 'Altech' # Model name
  serie: 'AK300'        # Model name
  W: 12.5               # Package width
  H: 12.5               # Package height
  WD: 6.5               # > Y distance form pin center to package edge
  A1: 0.1               # package board separation
  pin_number: [ 2,3,4,5,6,7,8,9,10,11,12,13,14,15,16,17,18,19,20,21,22,23,24]  # Which pin configuration
  PE: 2.5               # Distance from edge to pin
  PS: 5.0               # Distance between pins
  PD: [1.0, 0.8]        # Pin size, [1.0] diameter 1 mm, [1.0, 0.8] rectangle 1.0x0.8
  PL: 4.5               # Pin length
  PF: 'rect'            # Pin form 'round' or 'rect'
  SW: 2.7               # Blender width
  DD: 1.5               # Drill diameter
  PD: 3.0               # Pad diameter
  rotation: 0           # Rotation if required
  dest_dir_3D_prefix: 'TerminalBlock_Altech.3dshapes'  # Destination directory
