speedypotato/chuni-lite/chunair/kicad-footprint-generator-master/scripts/tools/global_config_files/config_KLCv1.0.yaml

3d_model_prefix: '${KISYS3DMOD}/'

silk_line_width: 0.15
silk_pad_clearance: 0.2
silk_fab_offset: 0.15
silk_line_length_min: 0.4
allow_silk_below_part: 'tht' # tht | smd | all | none

fab_line_width: 0.15
fab_pin1_marker_length: 1

courtyard_line_width: 0.05
courtyard_grid: 0.01
courtyard_offset:
    default: 0.25
    connector: 0.5
    bga: 1

edge_cuts_line_width: 0.12

references:
    -
          layer: 'F.Fab'
          position_y: 'top' # outside_top | inside | outside_bottom
          size: [2,2]
          fontwidth: 0.15
values:
    -
          layer: 'F.Fab'
          position_y: 'bottom' # outside_top | inside | outside_bottom
          size: [1,1]
          fontwidth: 0.15
